doomedramen/ch9121-rack-mount/renders/panel_fit.png

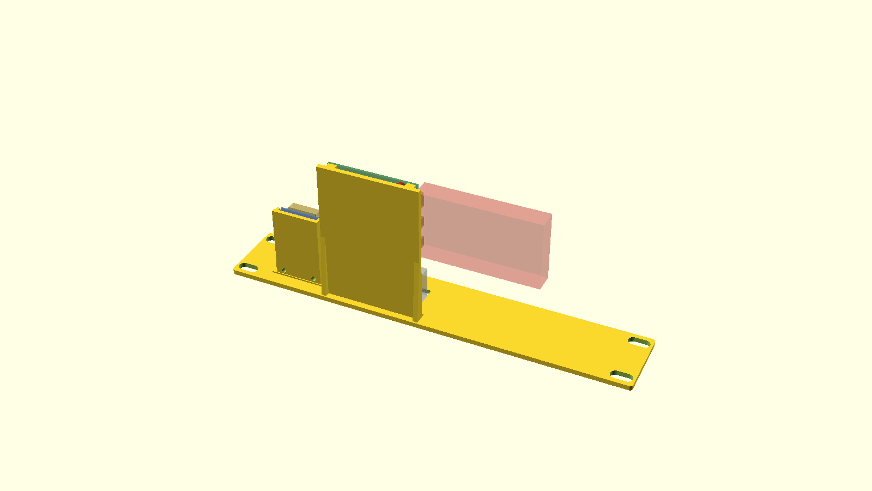
renders/panel_fit.png
